dgaff/dart_scoreboard/images/IMG_7865.jpeg

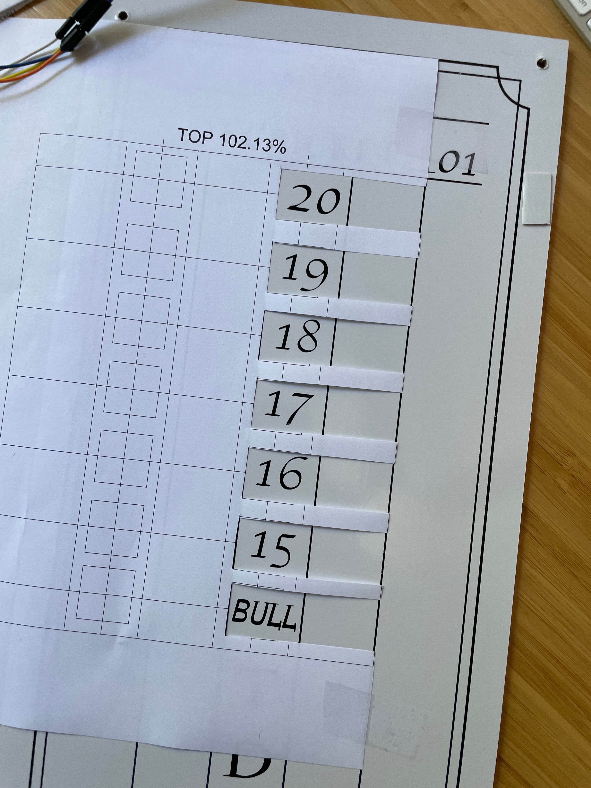
images/IMG_7865.jpeg
