dgaff/dart_scoreboard/images/IMG_7867.jpeg

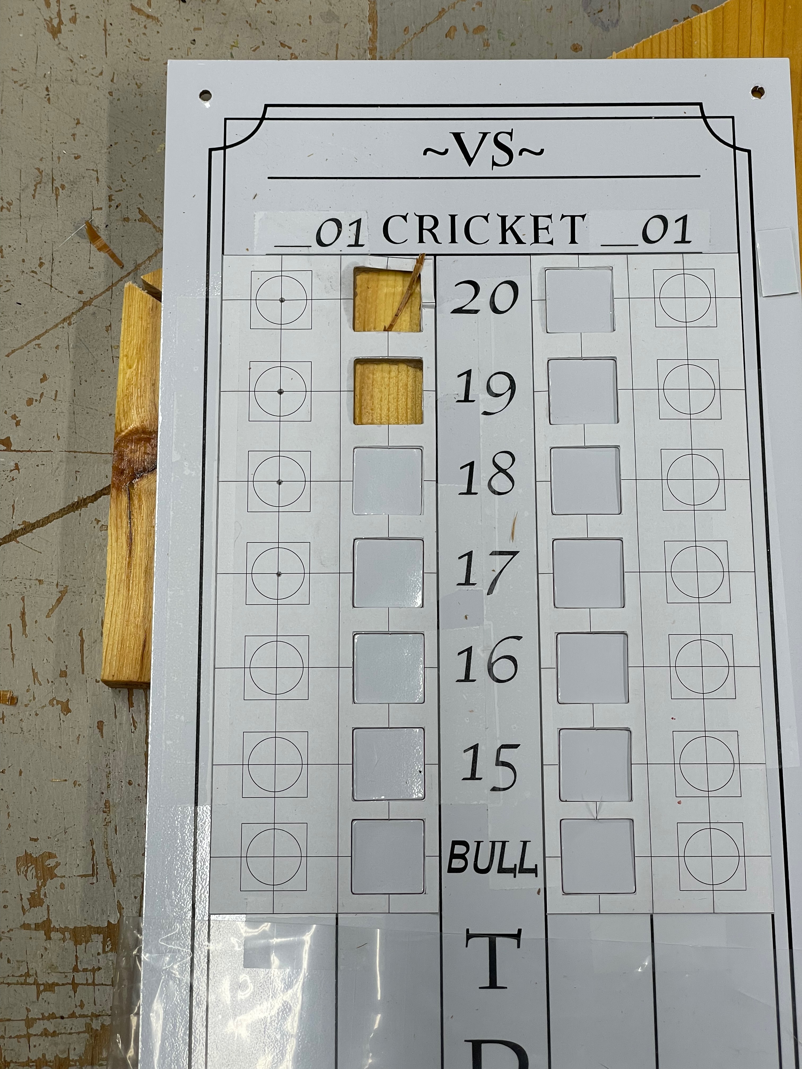
images/IMG_7867.jpeg
