dgaff/dart_scoreboard/images/IMG_8078.jpeg

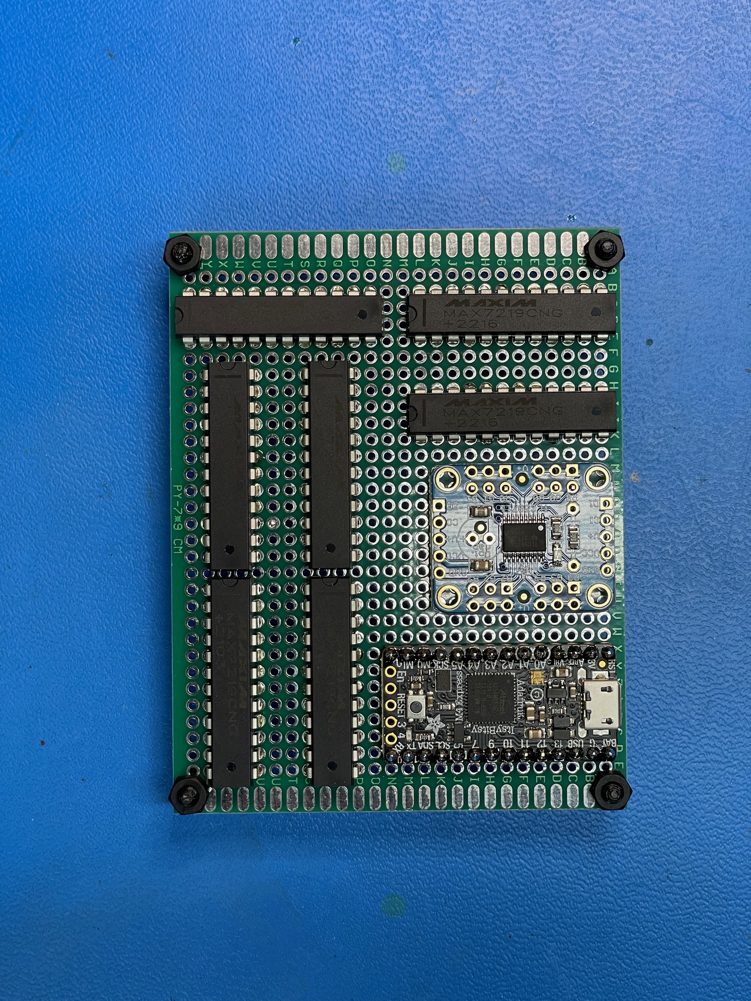
images/IMG_8078.jpeg
