dgaff/dart_scoreboard/images/IMG_8328.jpeg

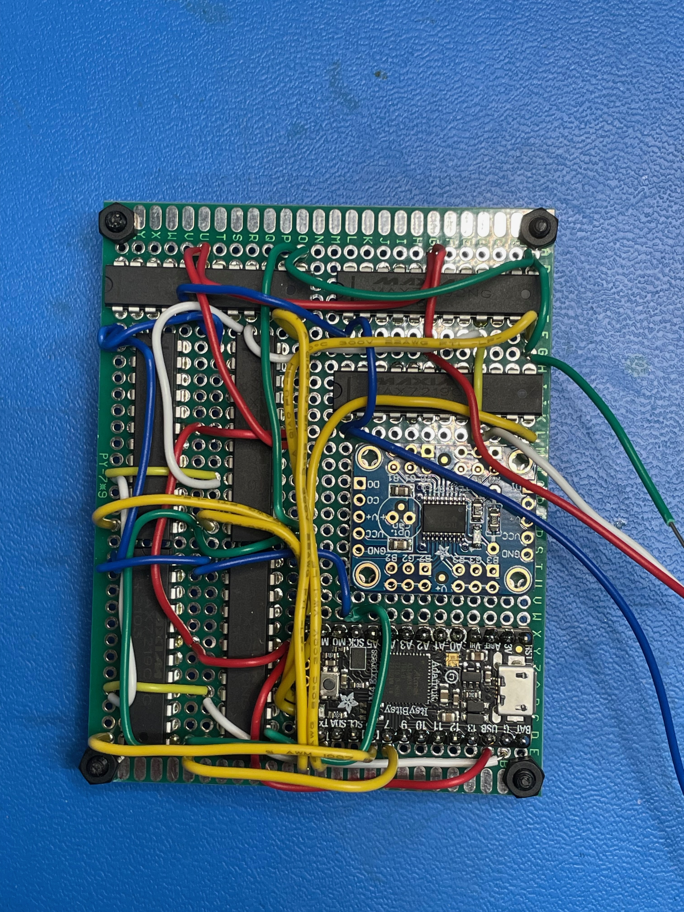
images/IMG_8328.jpeg
