dgaff/dart_scoreboard/images/IMG_9347.gif

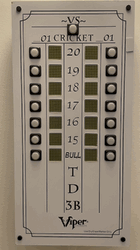
images/IMG_9347.gif
